KryptonPlusPlus/AVR-Pong/documentation/schematic/avr pong.kicad_sch

## KiCad design documentation/schematic/avr pong.kicad_sch (2025-02-24)

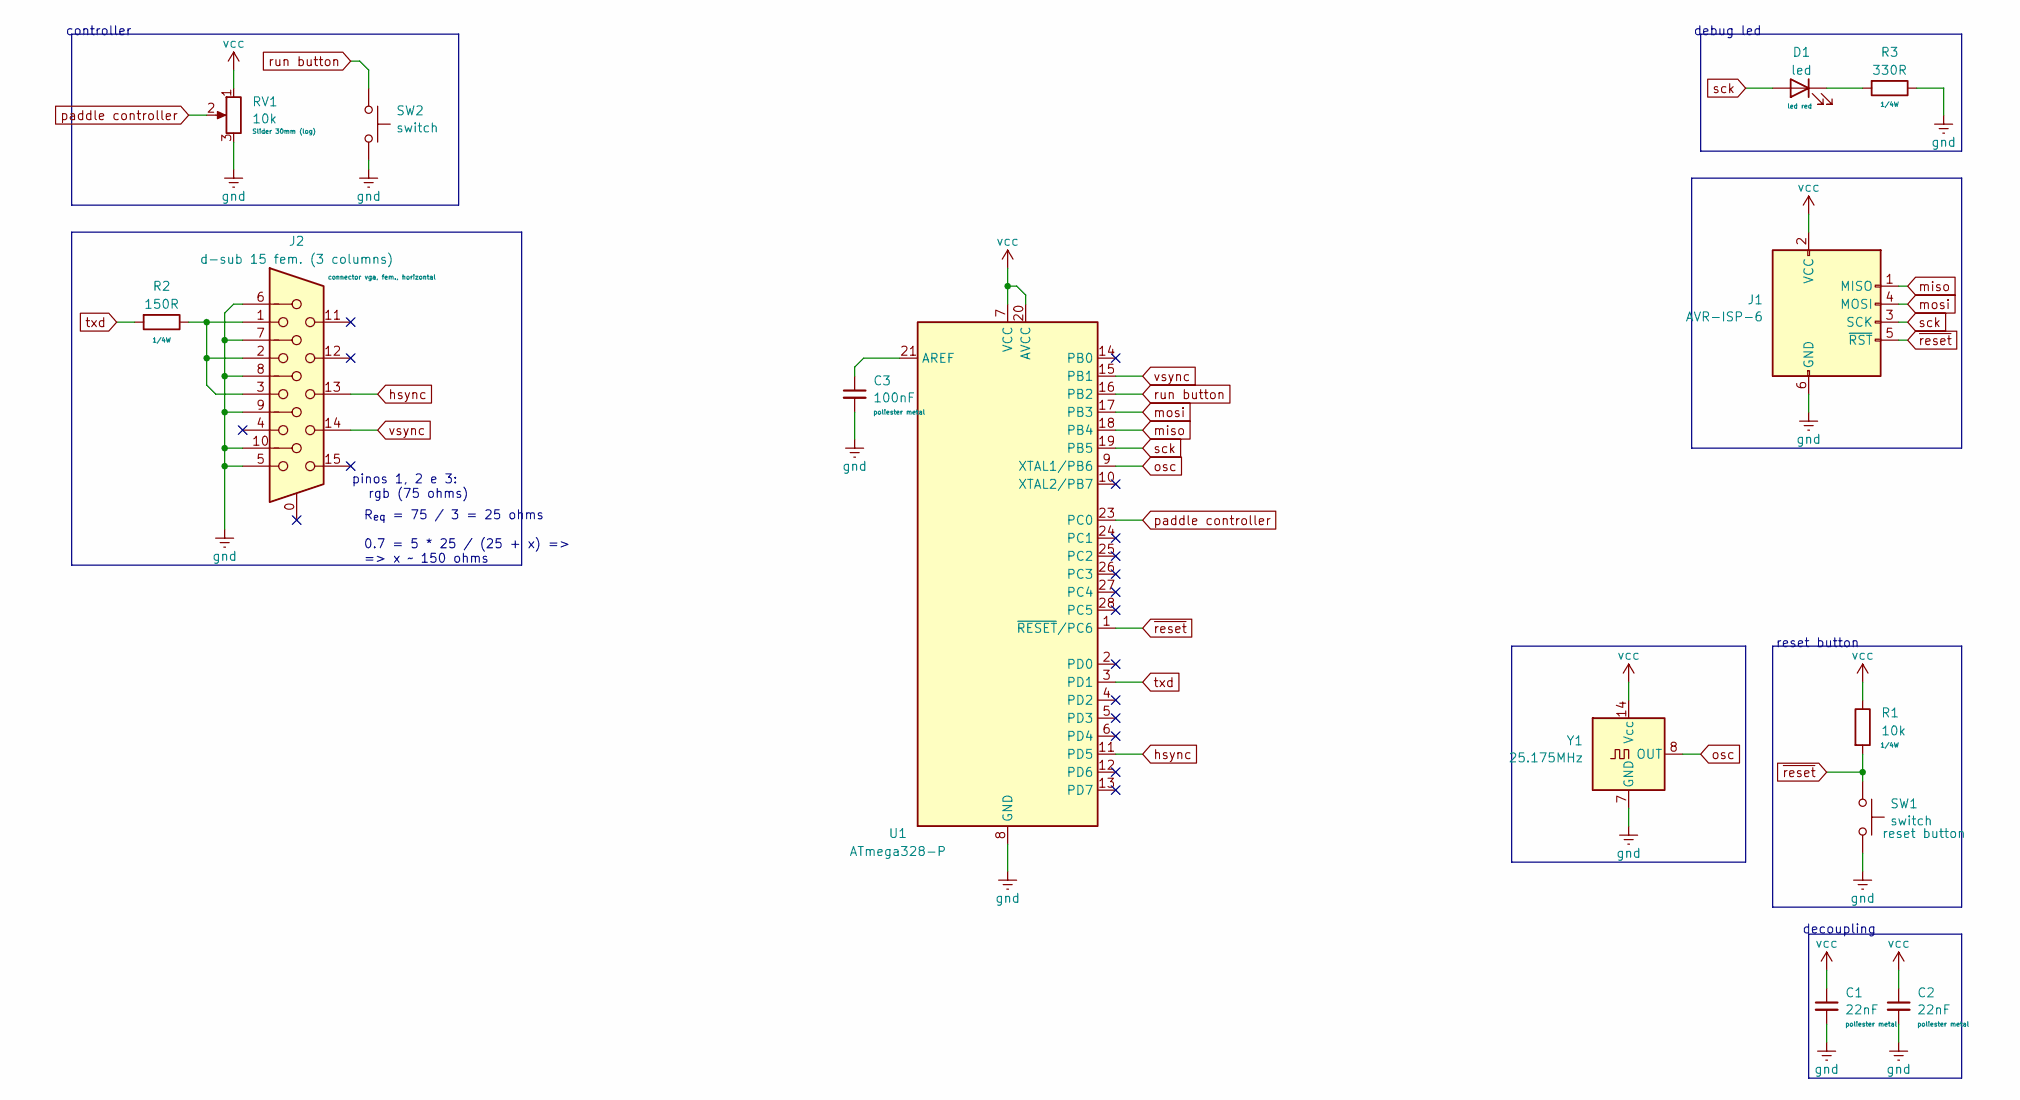
[picture p4: schematic avr pong.kicad_sch]

Parts:
C1, C2: 22nF; C_Rect_L7.0mm_W2.5mm_P5.00mm
C3: 100nF; C_Rect_L7.0mm_W2.5mm_P5.00mm
D1: led; LED_Rectangular_W5.0mm_H2.0mm
J1: AVR-ISP-6; IDC-Header_2x03_P2.54mm_Vertical
J2: d-sub 15 fem. (3 columns); DSUB-15-HD_Female_Horizontal_P2.29x2.54mm_EdgePinOffset8.35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
R1: 10k; R_Axial_DIN0207_L6.3mm_D2.5mm_P10.16mm_Horizontal
R2: 150R; R_Axial_DIN0207_L6.3mm_D2.5mm_P10.16mm_Horizontal
R3: 330R; R_Axial_DIN0207_L6.3mm_D2.5mm_P10.16mm_Horizontal
RV1: 10k; Potentiometer_Bourns_PTA3043_Single_Slide
SW1, SW2: switch; SW_PUSH_6mm_H4.3mm
U1: ATmega328-P; DIP-28_W7.62mm
Y1: 25.175MHz; Oscillator_DIP-14

Connections:
unnamed: C3.1, U1.21 (AREF)
unnamed: D1.1 (K), R3.2
unnamed: J2.1, J2.2, J2.3, R2.1
gnd: C1.2, C2.2, C3.2, J1.6 (GND), J2.5, J2.6, J2.7, J2.8, J2.9, J2.10, R3.1, RV1.3, SW1.2, SW2.2, U1.8 (GND), U1.22 (GND), Y1.7 (GND)
hsync: J2.13, U1.11 (PD5)
miso: J1.1 (MISO), U1.18 (PB4)
mosi: J1.4 (MOSI), U1.17 (PB3)
osc: U1.9 (XTAL1/PB6), Y1.8 (OUT)
paddle controller: RV1.2, U1.23 (PC0)
run button: SW2.1, U1.16 (PB2)
sck: D1.2 (A), J1.3 (SCK), U1.19 (PB5)
txd: R2.2, U1.3 (PD1)
vcc: C1.1, C2.1, J1.2 (VCC), R1.1, RV1.1, U1.7 (VCC), U1.20 (AVCC), Y1.14 (Vcc)
vsync: J2.14, U1.15 (PB1)
~reset: J1.5 (~RST), R1.2, SW1.1, U1.1 (~RESET/PC6)

Notes on the sheet:
controller
R_{eq} = 75 / 3 = 25 ohms 0.7 = 5 * 25 / (25 + x) => => x ~ 150 ohms
reset button
pinos 1, 2 e 3: rgb (75 ohms)
decoupling
debug led
